Schnilz/FW-EC-PSP-Joy/firmware/gamepad_config.h

#ifndef _GAMEPAD_CONFIG_H
#define _GAMEPAD_CONFIG_H

#define GAMEPAD_LOGICAL_MIN (0)
#define GAMEPAD_LOGICAL_MAX (0xFF - 1)

#define STR_MANUFACTURER u"schnils"
#define STR_PRODUCT u"Framwork Gamepad"


#endif
